HiSER/SirenaBT5/sirena_uart/uart_doc/config_newline.png

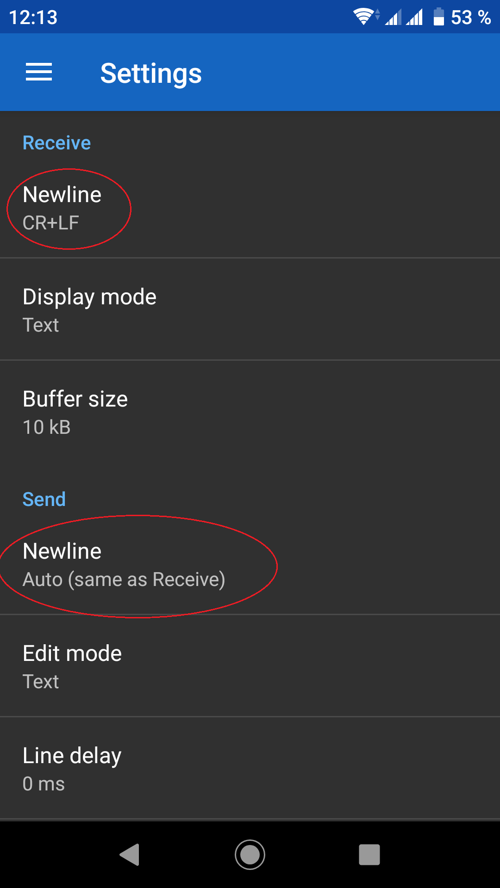
sirena_uart/uart_doc/config_newline.png
