HiSER/SirenaBT5/sirena_uart/uart_doc/on_uart.png

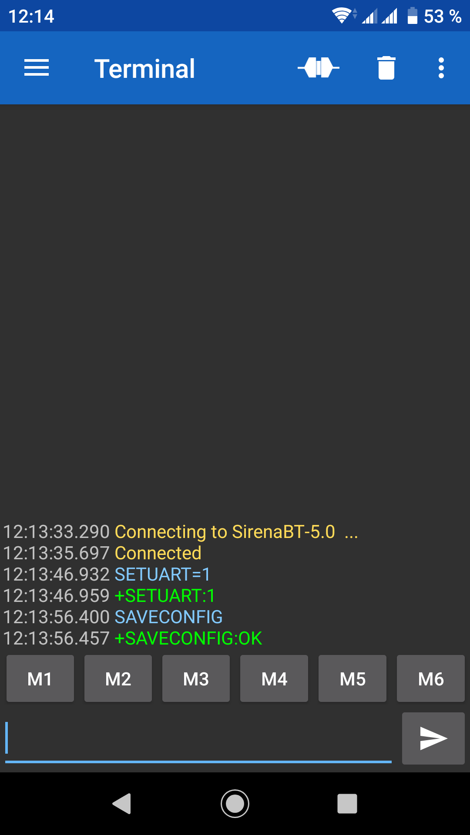
sirena_uart/uart_doc/on_uart.png
