HiSER/SirenaBT5/sirena_uart/uart_doc/select_device.png

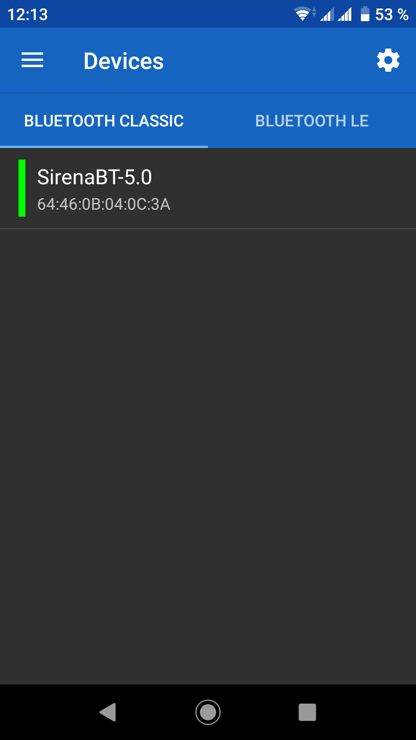
sirena_uart/uart_doc/select_device.png
