HiSER/SirenaBT5/sirena_uart/uart_doc/terminal.png

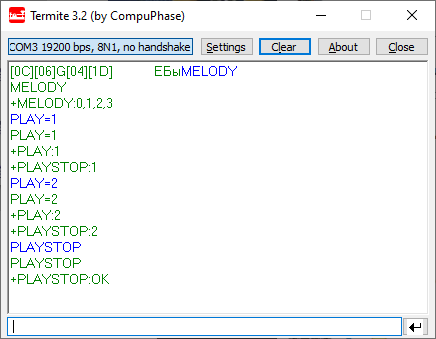
sirena_uart/uart_doc/terminal.png
