HiSER/SirenaBT5/PCB/SirenaBT5-bottom-components.png

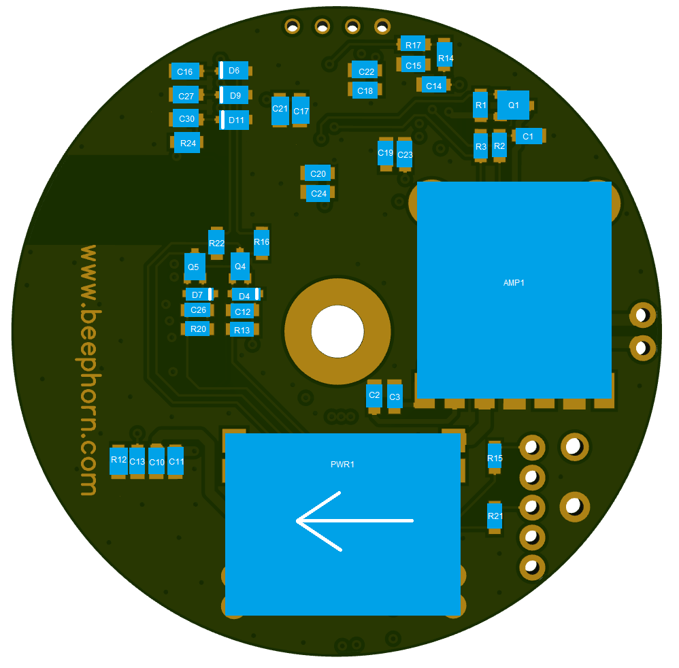
PCB/SirenaBT5-bottom-components.png
