HiSER/SirenaBT5/PCB/SirenaBT5-top-components.png

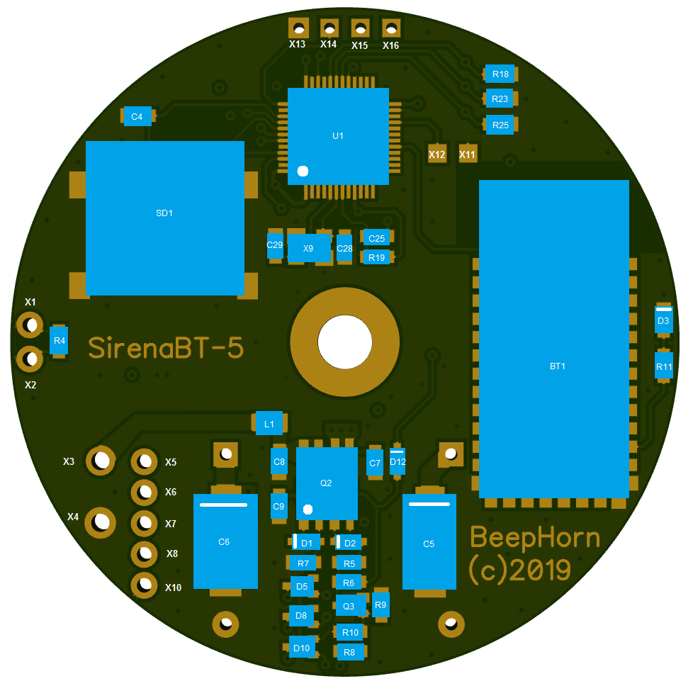
PCB/SirenaBT5-top-components.png
